ElMikosch/quiz-buzzer/src/main.cpp

// Entry point for quiz buzzer system
// This file is intentionally empty - the actual implementation
// is in buzzer_node.cpp or controller.cpp, selected by build_src_filter
// in platformio.ini based on the environment being built.
